Challenger3000/ANTWEIGHT_BATTLEBOT/brain_2.2/pid.ino

void init_pid(){
  Setpoint = 0.0;
  myPID.SetMode(AUTOMATIC);
  myPID.SetOutputLimits(-2048,2048);
  myPID.SetTunings(EEPROM_DATA.PID_P,EEPROM_DATA.PID_I,EEPROM_DATA.PID_D);
  myPID.SetSampleTime(1);
  // Serial.print("EEPROM PID PARAMS P: ");
  // Serial.print(EEPROM_DATA.PID_P);
  // Serial.print("\tI: ");
  // Serial.print(EEPROM_DATA.PID_I);
  // Serial.print("\tD: ");
  // Serial.println(EEPROM_DATA.PID_D);
}

void update_pid(){

  if(accelData.accelZ > 0){
    Input = (double) filtered_signal;
  }else{
    Input = (double) -filtered_signal;
  }

  myPID.Compute();
}
