Challenger3000/ANTWEIGHT_BATTLEBOT/brain_2.2/gpio.ino

void init_gpio(){
  pinMode(BUTTON, INPUT_PULLUP);
  pinMode(VSENSE, INPUT);
}

void update_gpio(){
  if(millis() - last_gpio_update > 100){

    // reboot if imu/pid lib overflows (happens every 71st minute cause of -micros() )
    if(motorA_output > 1000000000){
      ESP.restart();
    }

    check_servo_0_before_arming();
    last_gpio_update = millis();
    send_voltage_telemety();
    if(!digitalRead(BUTTON)){
      switch_wireles_mode();
    }
    esp_task_wdt_reset();                 // reset watchdog, to prevent reboot
    // imu_print();
  }
}
